DingLongya/HoloCubic/3.HoloCubic_AIO多功能上位机v1.4.5/AIO固件_放置到内存卡(测试图片及视频)/image/VCG211143798603.jpg

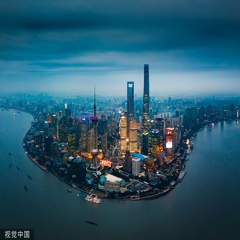
3.HoloCubic_AIO多功能上位机v1.4.5/AIO固件_放置到内存卡(测试图片及视频)/image/VCG211143798603.jpg
