DingLongya/HoloCubic/3.HoloCubic_AIO多功能上位机v1.4.5/HoloCubic_AIO_Tool.png

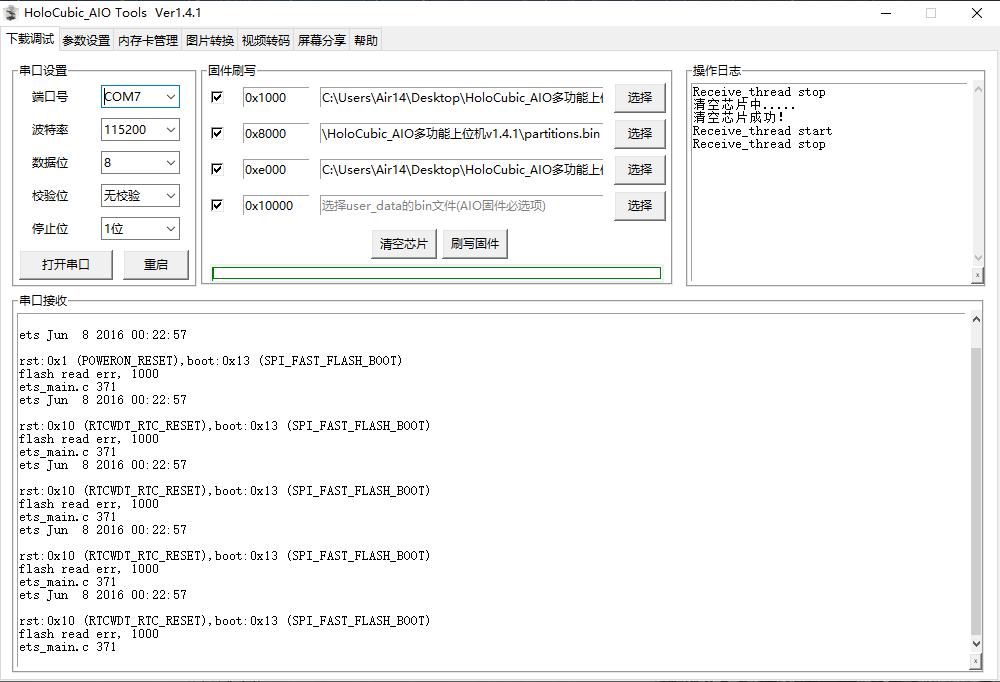
3.HoloCubic_AIO多功能上位机v1.4.5/HoloCubic_AIO_Tool.png
