DingLongya/HoloCubic/3.HoloCubic_AIO多功能上位机v1.4.5/OutFile/Cache/www.jpg

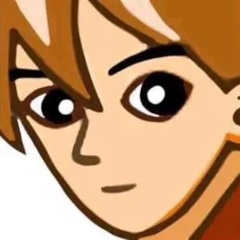
3.HoloCubic_AIO多功能上位机v1.4.5/OutFile/Cache/www.jpg
