DingLongya/HoloCubic/3.HoloCubic_AIO多功能上位机v1.4.5/投屏/IMG_20211224_193821.jpg

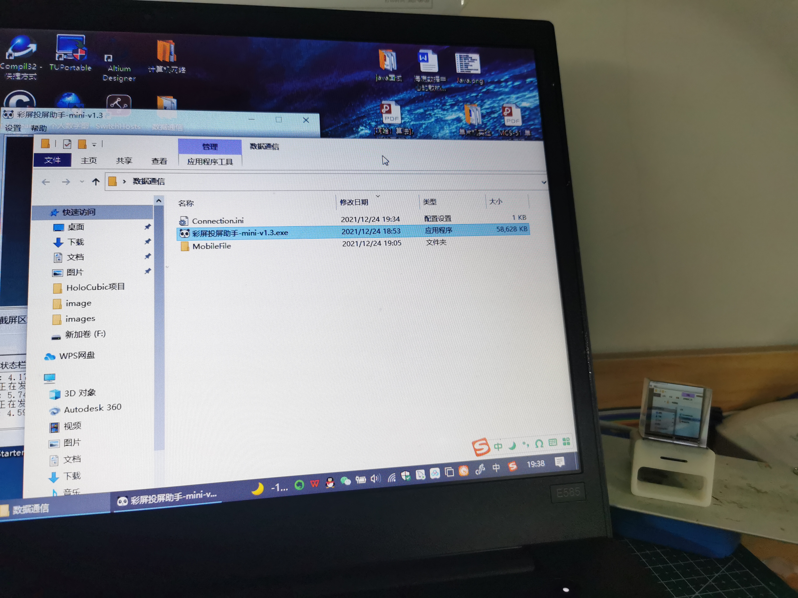
3.HoloCubic_AIO多功能上位机v1.4.5/投屏/IMG_20211224_193821.jpg
