DingLongya/HoloCubic/4_2.提交的 3D Model/效果.jpg

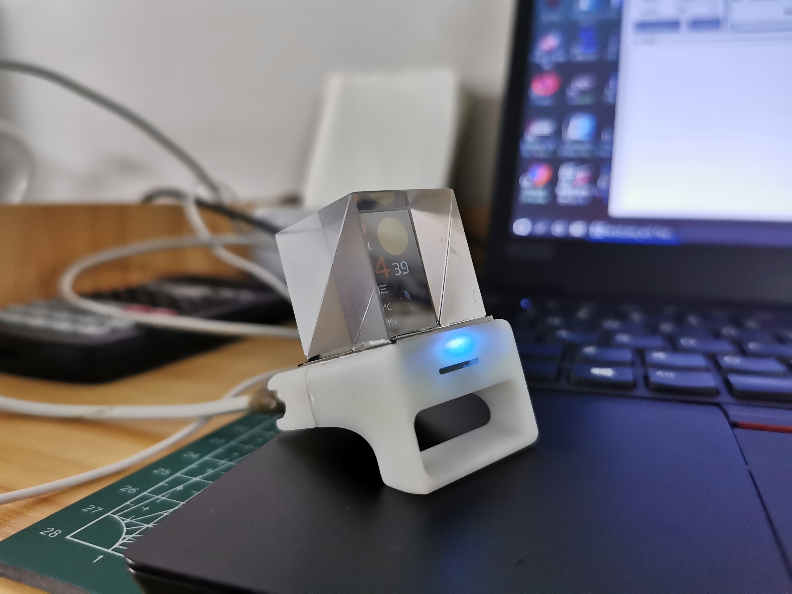
4_2.提交的 3D Model/效果.jpg
